PiKeeb/lyra-keyboard/pcb_design/lyra_alpha/lyra_alpha.kicad_sch

## KiCad design pcb_design/lyra_alpha/lyra_alpha.kicad_sch (2021-06-27)

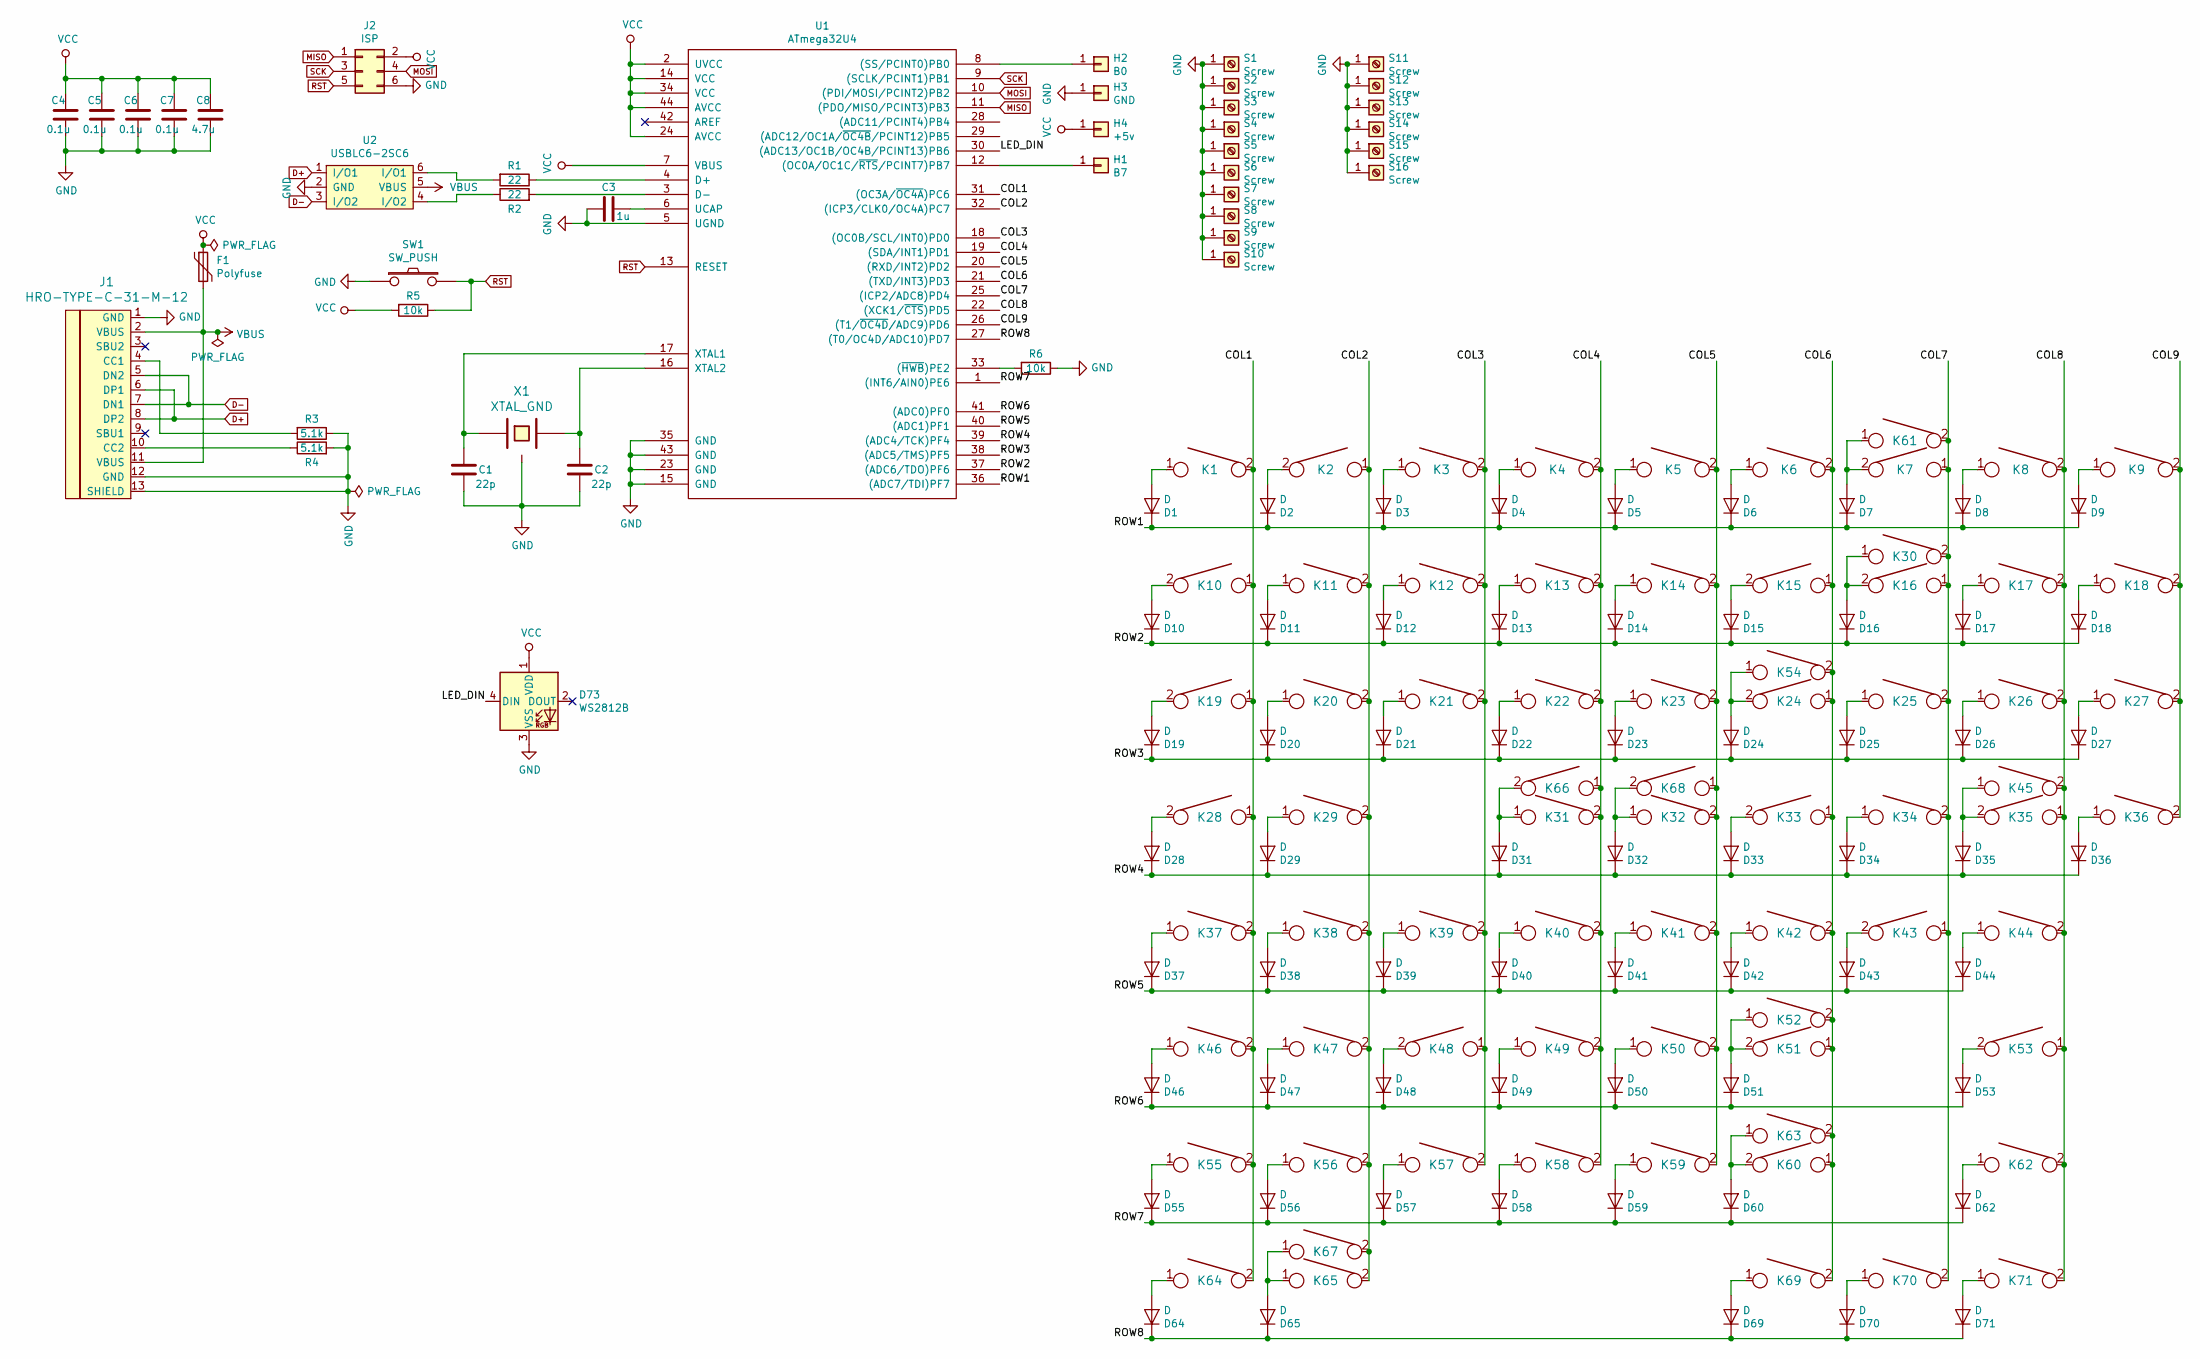
[picture p6: schematic lyra_alpha.kicad_sch]

Parts:
C1, C2: 22p; C_0805
C3: 1u; C_0805
C4, C5, C6, C7: 0.1u; C_0805
C8: 4.7u; C_0805
D1, D2, D3, D4, D5, D6, D7, D8, D9, D10, D11, D12, D13, D14, D15, D16, D17, D18, D19, D20, D21, D22, D23, D24, D25, D26, D27, D28, D29, D31, D32, D33, D34, D35, D36, D37, D38, D39, D40, D41, D42, D43, D44, D46, D47, D48, D49, D50, D51, D53, D55, D56, D57, D58, D59, D60, D62, D64, D65, D69, D70, D71: D; D_0805_2012Metric_Pad1.15x1.40mm_HandSolder
D73: WS2812B; LED_WS2812B_PLCC4_5.0x5.0mm_P3.2mm
F1: Polyfuse; R_0805
H1: B7; free_pin
H2: B0; free_pin
H3: GND; free_pin
H4: +5v; free_pin
J1: HRO-TYPE-C-31-M-12
J2: ISP; isp_standard
K1, K2, K3, K4, K5, K6, K7, K8, K9, K10, K11, K12, K13, K14, K15, K16, K17, K18, K19, K20, K21, K22, K23, K24, K25, K26, K27, K28, K29, K30, K31, K32, K33, K34, K35, K36, K37, K38, K39, K40, K41, K42, K43, K44, K45, K46, K47, K48, K49, K50, K51, K52, K53, K54, K55, K56, K57, K58, K59, K60, K61, K62, K63, K64, K65, K66, K67, K68, K69, K70, K71: KEYSW; Kailh_socket
R1, R2: 22; R_0805
R3, R4: 5.1k; R_0805
R5, R6: 10k; R_0805
S1, S2, S3, S4, S5, S6, S7, S8, S9, S10: Screw; 52hole48
S11: Screw; cherry_6.25u_PCB
S12, S13: Screw; SW_Cherry_MX1A_2.00u_PCB
S14: Screw; SW_Cherry_MX1A_2.25u_PCB
S15, S16: Screw; SW_Cherry_MX1A_2.75u_PCB
SW1: SW_PUSH; SW_SPST_TL3342
U1: ATmega32U4; ATMEGA32U4
U2: USBLC6-2SC6; Farnell 1295310
X1: XTAL_GND; crystal_FA238-TSX3225

Connections:
COL1: K1.2, K10.1, K19.1, K28.1, K37.2, K46.2, K55.2, K64.2, U1.31 ((OC3A/~OC4A~)PC6)
COL2: K2.1, K11.2, K20.2, K29.2, K38.2, K47.2, K56.2, K65.2, K67.2, U1.32 ((ICP3/CLK0/OC4A)PC7)
COL3: K3.2, K12.2, K21.2, K39.2, K48.1, K57.2, U1.18 ((OC0B/SCL/INT0)PD0)
COL4: K4.2, K13.2, K22.2, K31.2, K40.2, K49.2, K58.2, K66.1, U1.19 ((SDA/INT1)PD1)
COL5: K5.2, K14.2, K23.2, K32.2, K41.2, K50.2, K59.2, K68.1, U1.20 ((RXD/INT2)PD2)
COL6: K6.2, K15.1, K24.1, K33.1, K42.2, K51.1, K52.2, K54.2, K60.1, K63.2, K69.2, U1.21 ((TXD/INT3)PD3)
COL7: K7.1, K16.1, K25.2, K30.2, K34.2, K43.1, K61.2, K70.2, U1.25 ((ICP2/ADC8)PD4)
COL8: K8.2, K17.2, K26.2, K35.1, K44.2, K45.2, K53.1, K62.2, K71.2, U1.22 ((XCK1/~CTS~)PD5)
COL9: K9.2, K18.2, K27.2, K36.2, U1.26 ((T1/~OC4D~/ADC9)PD6)
D+: J1.6 (DP1), J1.8 (DP2), U2.1 (I/O1)
D-: J1.5 (DN2), J1.7 (DN1), U2.3 (I/O2)
GND: C1.1, C2.1, C3.2, C4.1, C5.1, C6.1, C7.1, C8.1, D73.3 (VSS), H3.1, J1.1 (GND), J1.12 (GND), J1.13 (SHIELD), J2.6, R3.1, R4.2, R6.1, S1.1, S2.1, S3.1, S4.1, S5.1, S6.1, S7.1, S8.1, S9.1, S10.1, S11.1, S12.1, S13.1, S14.1, S15.1, S16.1, SW1.1, U1.5 (UGND), U1.15 (GND), U1.23 (GND), U1.35 (GND), U1.43 (GND), U2.2 (GND), X1.3
LED_DIN: D73.4 (DIN), U1.30 ((ADC13/OC1B/OC4B/PCINT13)PB6)
MISO: J2.1, U1.11 ((PDO/MISO/PCINT3)PB3)
MOSI: J2.4, U1.10 ((PDI/MOSI/PCINT2)PB2)
unnamed: C1.2, U1.17 (XTAL1), X1.1
unnamed: C2.2, U1.16 (XTAL2), X1.2
unnamed: C3.1, U1.6 (UCAP)
unnamed: D1.2 (A), K1.1
unnamed: D2.2 (A), K2.2
unnamed: D3.2 (A), K3.1
unnamed: D4.2 (A), K4.1
unnamed: D5.2 (A), K5.1
unnamed: D6.2 (A), K6.1
unnamed: D7.2 (A), K7.2, K61.1
unnamed: D8.2 (A), K8.1
unnamed: D9.2 (A), K9.1
unnamed: D10.2 (A), K10.2
unnamed: D11.2 (A), K11.1
unnamed: D12.2 (A), K12.1
unnamed: D13.2 (A), K13.1
unnamed: D14.2 (A), K14.1
unnamed: D15.2 (A), K15.2
unnamed: D16.2 (A), K16.2, K30.1
unnamed: D17.2 (A), K17.1
unnamed: D18.2 (A), K18.1
unnamed: D19.2 (A), K19.2
unnamed: D20.2 (A), K20.1
unnamed: D21.2 (A), K21.1
unnamed: D22.2 (A), K22.1
unnamed: D23.2 (A), K23.1
unnamed: D24.2 (A), K24.2, K54.1
unnamed: D25.2 (A), K25.1
unnamed: D26.2 (A), K26.1
unnamed: D27.2 (A), K27.1
unnamed: D28.2 (A), K28.2
unnamed: D29.2 (A), K29.1
unnamed: D31.2 (A), K31.1, K66.2
unnamed: D32.2 (A), K32.1, K68.2
unnamed: D33.2 (A), K33.2
unnamed: D34.2 (A), K34.1
unnamed: D35.2 (A), K35.2, K45.1
unnamed: D36.2 (A), K36.1
unnamed: D37.2 (A), K37.1
unnamed: D38.2 (A), K38.1
unnamed: D39.2 (A), K39.1
unnamed: D40.2 (A), K40.1
unnamed: D41.2 (A), K41.1
unnamed: D42.2 (A), K42.1
unnamed: D43.2 (A), K43.2
unnamed: D44.2 (A), K44.1
unnamed: D46.2 (A), K46.1
unnamed: D47.2 (A), K47.1
unnamed: D48.2 (A), K48.2
unnamed: D49.2 (A), K49.1
unnamed: D50.2 (A), K50.1
unnamed: D51.2 (A), K51.2, K52.1
unnamed: D53.2 (A), K53.2
unnamed: D55.2 (A), K55.1
unnamed: D56.2 (A), K56.1
unnamed: D57.2 (A), K57.1
unnamed: D58.2 (A), K58.1
unnamed: D59.2 (A), K59.1
unnamed: D60.2 (A), K60.2, K63.1
unnamed: D62.2 (A), K62.1
unnamed: D64.2 (A), K64.1
unnamed: D65.2 (A), K65.1, K67.1
unnamed: D69.2 (A), K69.1
unnamed: D70.2 (A), K70.1
unnamed: D71.2 (A), K71.1
unnamed: H1.1, U1.12 ((OC0A/OC1C/~RTS~/PCINT7)PB7)
unnamed: H2.1, U1.8 ((SS/PCINT0)PB0)
unnamed: J1.4 (CC1), R3.2
unnamed: J1.10 (CC2), R4.1
unnamed: R1.1, U1.4 (D+)
unnamed: R1.2, U2.6 (I/O1)
unnamed: R2.1, U2.4 (I/O2)
unnamed: R2.2, U1.3 (D-)
unnamed: R6.2, U1.33 ((~HWB~)PE2)
ROW1: D1.1 (K), D2.1 (K), D3.1 (K), D4.1 (K), D5.1 (K), D6.1 (K), D7.1 (K), D8.1 (K), D9.1 (K), U1.36 ((ADC7/TDI)PF7)
ROW2: D10.1 (K), D11.1 (K), D12.1 (K), D13.1 (K), D14.1 (K), D15.1 (K), D16.1 (K), D17.1 (K), D18.1 (K), U1.37 ((ADC6/TDO)PF6)
ROW3: D19.1 (K), D20.1 (K), D21.1 (K), D22.1 (K), D23.1 (K), D24.1 (K), D25.1 (K), D26.1 (K), D27.1 (K), U1.38 ((ADC5/TMS)PF5)
ROW4: D28.1 (K), D29.1 (K), D31.1 (K), D32.1 (K), D33.1 (K), D34.1 (K), D35.1 (K), D36.1 (K), U1.39 ((ADC4/TCK)PF4)
ROW5: D37.1 (K), D38.1 (K), D39.1 (K), D40.1 (K), D41.1 (K), D42.1 (K), D43.1 (K), D44.1 (K), U1.40 ((ADC1)PF1)
ROW6: D46.1 (K), D47.1 (K), D48.1 (K), D49.1 (K), D50.1 (K), D51.1 (K), D53.1 (K), U1.41 ((ADC0)PF0)
ROW7: D55.1 (K), D56.1 (K), D57.1 (K), D58.1 (K), D59.1 (K), D60.1 (K), D62.1 (K), U1.1 ((INT6/AIN0)PE6)
ROW8: D64.1 (K), D65.1 (K), D69.1 (K), D70.1 (K), D71.1 (K), U1.27 ((T0/OC4D/ADC10)PD7)
RST: J2.5, R5.1, SW1.2, U1.13 (RESET)
SCK: J2.3, U1.9 ((SCLK/PCINT1)PB1)
VBUS: F1.2, J1.2 (VBUS), J1.11 (VBUS), U2.5 (VBUS)
VCC: C4.2, C5.2, C6.2, C7.2, C8.2, D73.1 (VDD), F1.1, H4.1, J2.2, R5.2, U1.2 (UVCC), U1.7 (VBUS), U1.14 (VCC), U1.24 (AVCC), U1.34 (VCC), U1.44 (AVCC)
